meerstern/USBSerial_I2C_Converter/SampleNodeRedFlow/Node-Red_ADC121C021.jpg

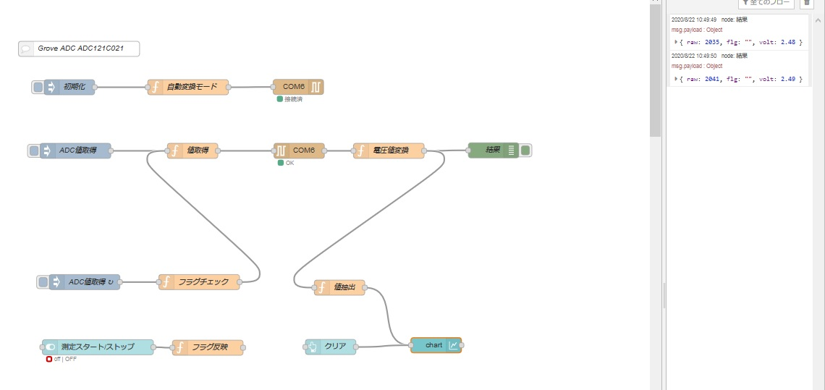
SampleNodeRedFlow/Node-Red_ADC121C021.jpg
