meerstern/USBSerial_I2C_Converter/SampleNodeRedFlow/Node-Red_AMG8833.png

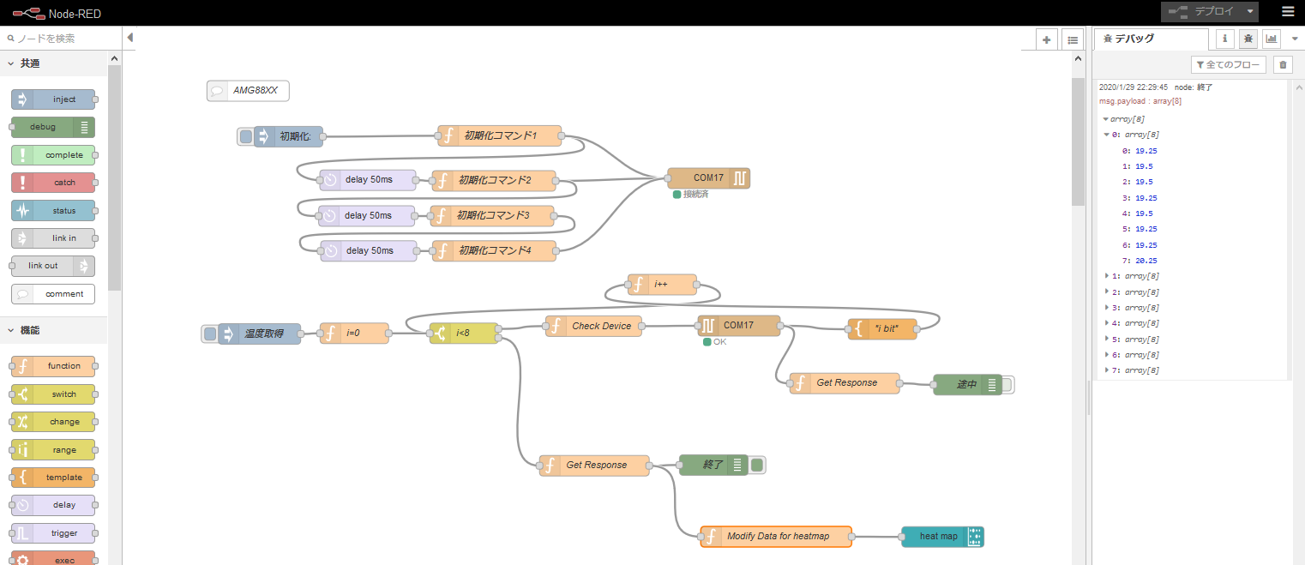
SampleNodeRedFlow/Node-Red_AMG8833.png
