meerstern/USBSerial_I2C_Converter/SampleNodeRedFlow/Node-Red_CCS811.jpg

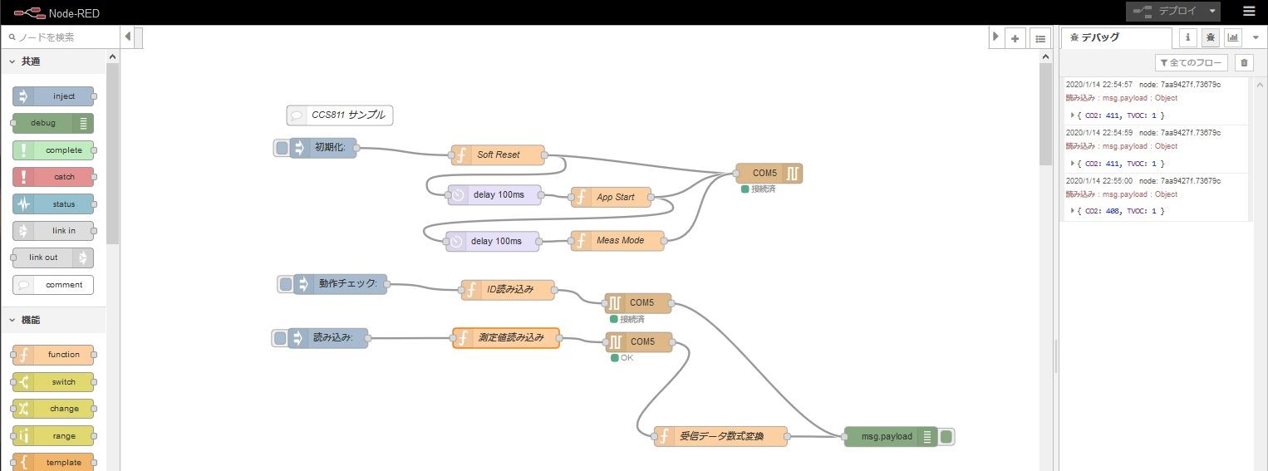
SampleNodeRedFlow/Node-Red_CCS811.jpg
