meerstern/USBSerial_I2C_Converter/SampleNodeRedFlow/Node-Red_EEPROM_24LCXXX_flows.jpg

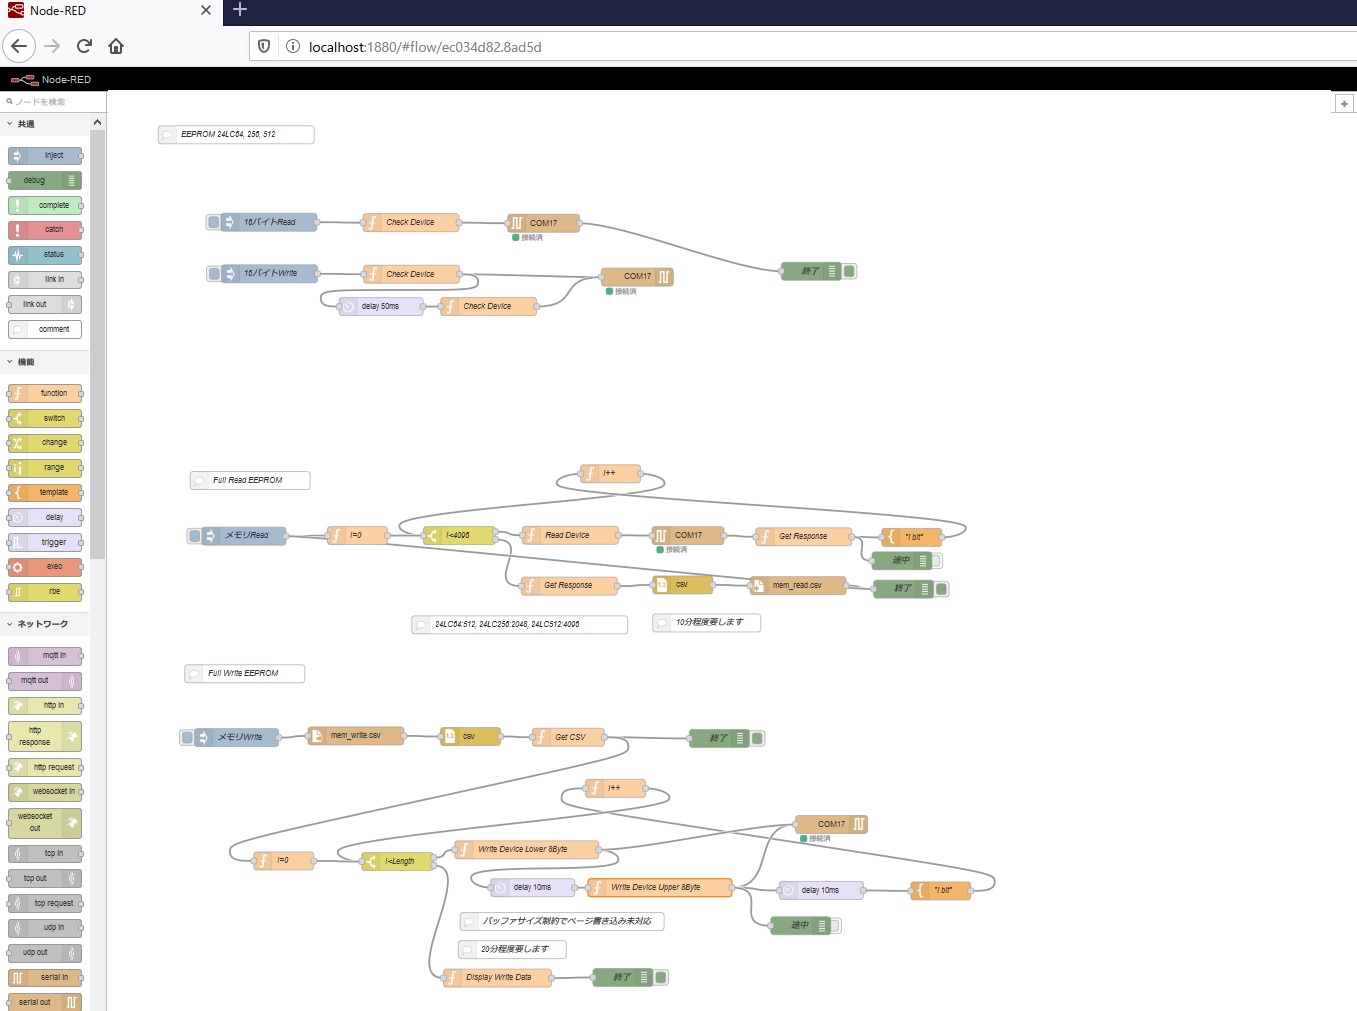
SampleNodeRedFlow/Node-Red_EEPROM_24LCXXX_flows.jpg
