meerstern/USBSerial_I2C_Converter/SampleNodeRedFlow/Node-Red_GPIO.jpg

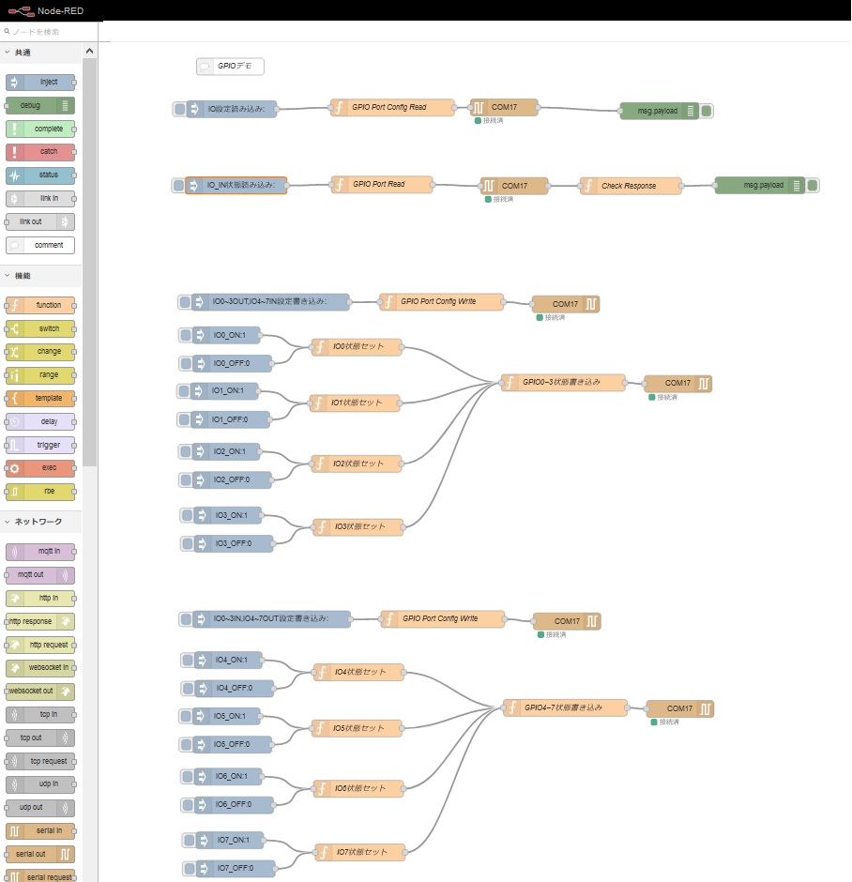
SampleNodeRedFlow/Node-Red_GPIO.jpg
