meerstern/USBSerial_I2C_Converter/SampleNodeRedFlow/Node-Red_I2Cdevicesearch.jpg

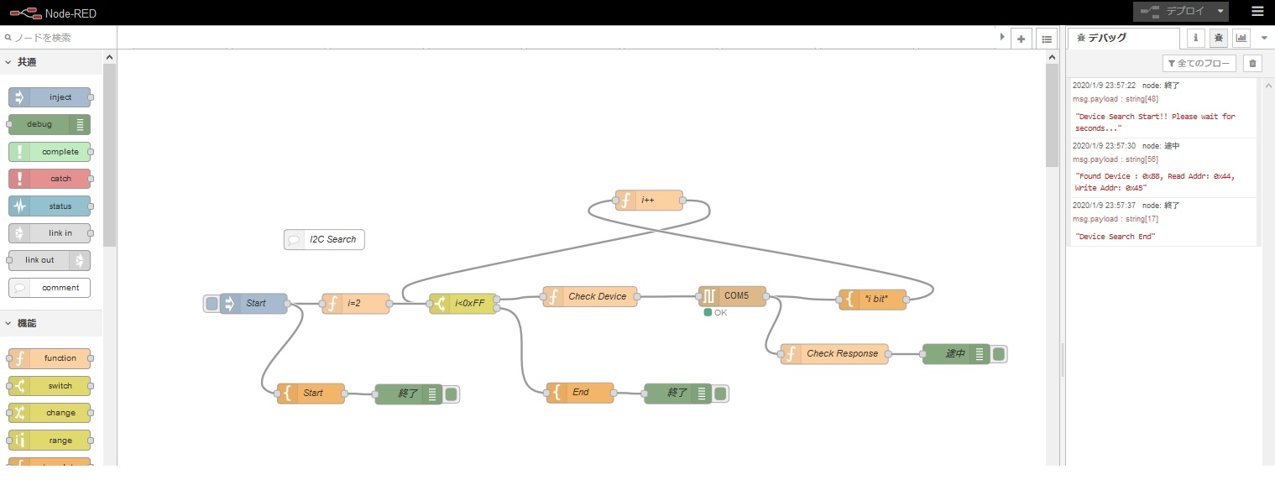
SampleNodeRedFlow/Node-Red_I2Cdevicesearch.jpg
