meerstern/USBSerial_I2C_Converter/SampleNodeRedFlow/Node-Red_MLX90614.jpg

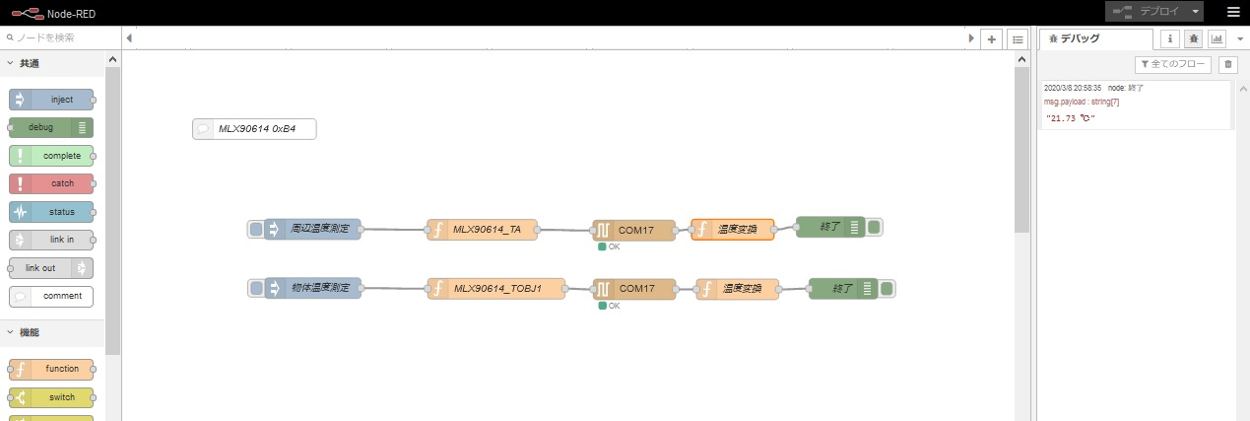
SampleNodeRedFlow/Node-Red_MLX90614.jpg
