meerstern/USBSerial_I2C_Converter/SampleNodeRedFlow/Node-Red_RV-8803-C7.jpg

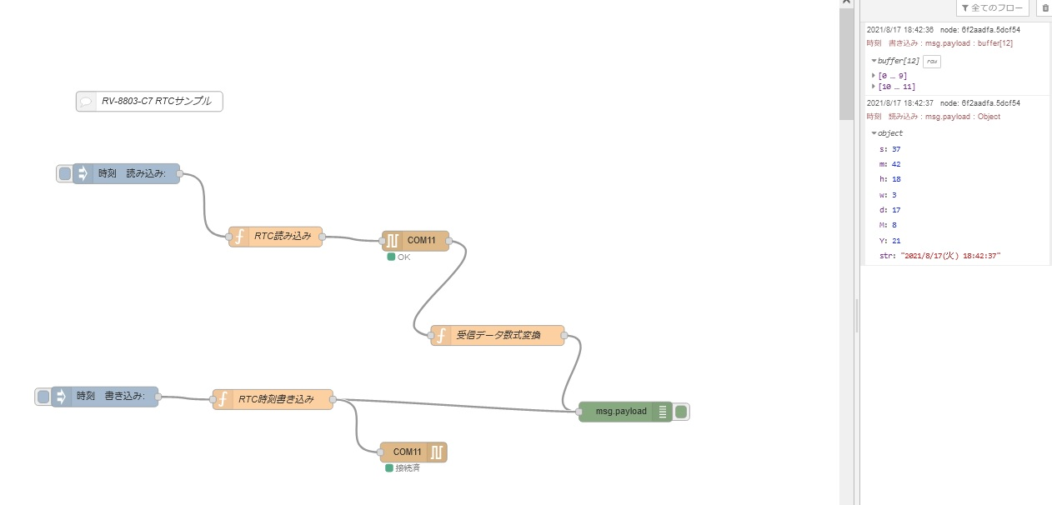
SampleNodeRedFlow/Node-Red_RV-8803-C7.jpg
