meerstern/USBSerial_I2C_Converter/SampleNodeRedFlow/Node-Red_VL53L0.jpg

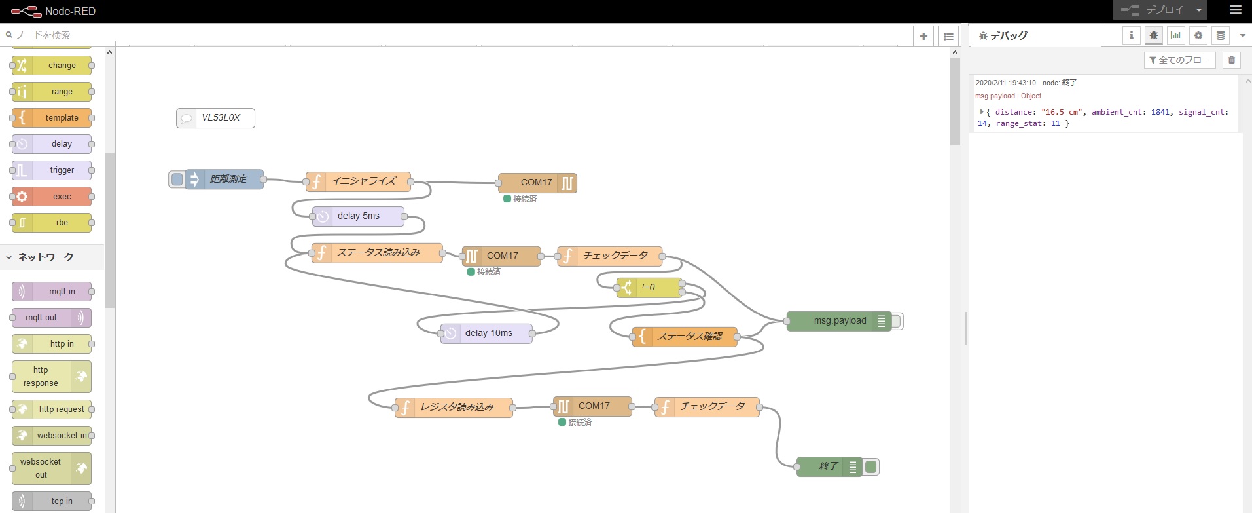
SampleNodeRedFlow/Node-Red_VL53L0.jpg
