meerstern/USBSerial_I2C_Converter/SampleNodeRedFlow/Node-Red_VL53L1.jpg

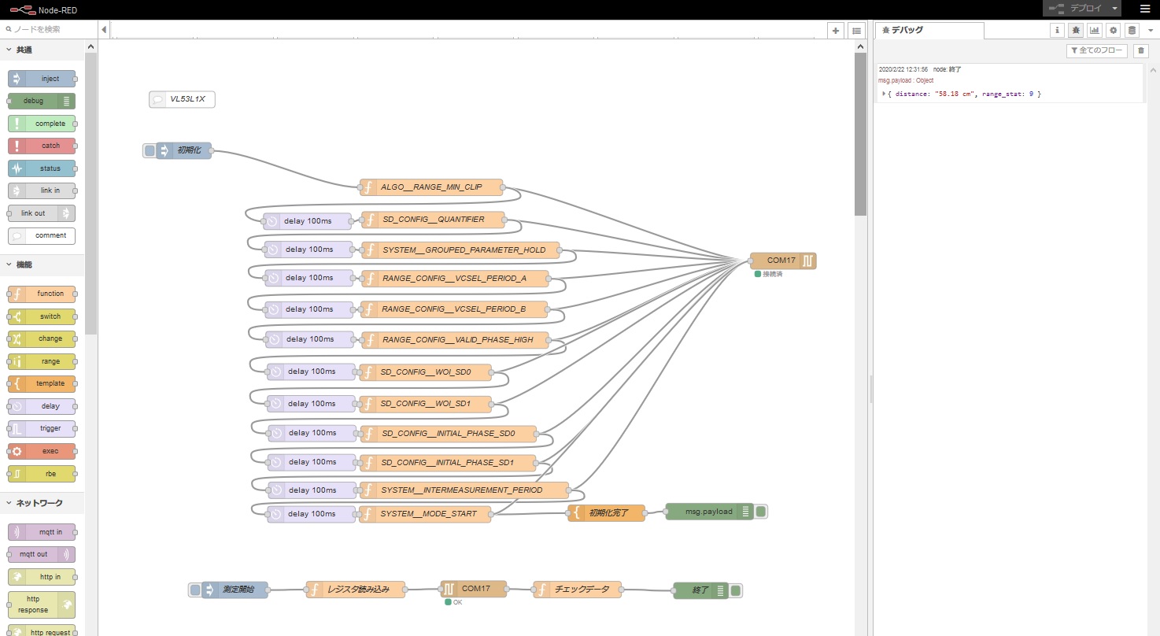
SampleNodeRedFlow/Node-Red_VL53L1.jpg
